KOINSLOT-Inc/kywy-hardware/PCB/Renders/Rotation/Kywy Micro Rotation 01.png

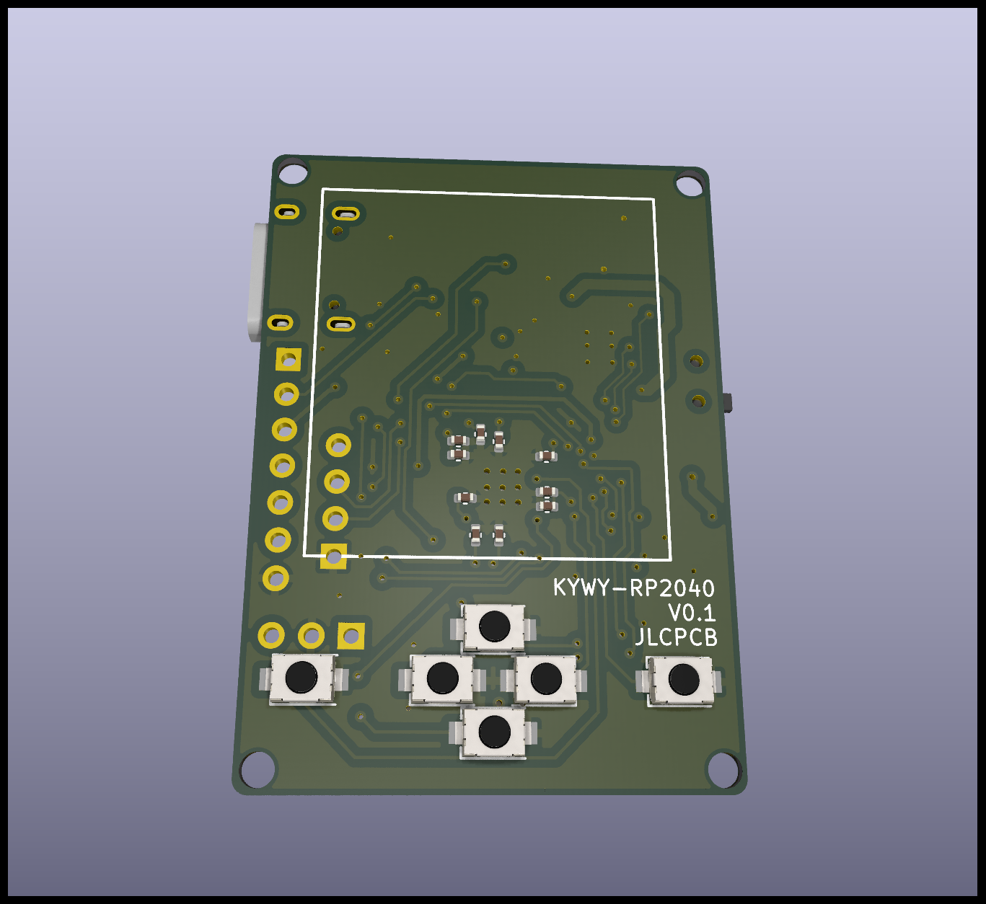
PCB/Renders/Rotation/Kywy Micro Rotation 01.png
