KOINSLOT-Inc/kywy-hardware/PCB/Renders/Rotation/Kywy Micro Rotation 02.png

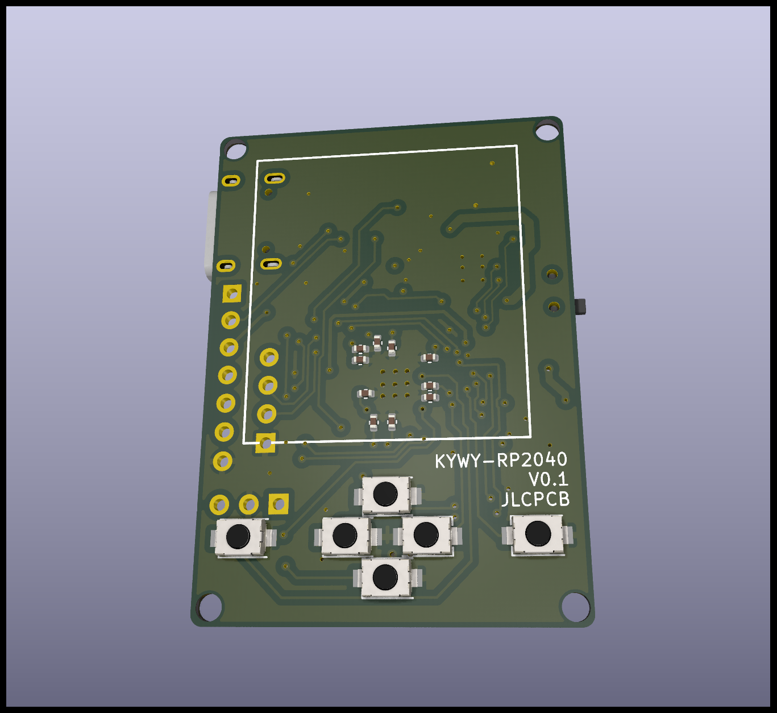
PCB/Renders/Rotation/Kywy Micro Rotation 02.png
