KOINSLOT-Inc/kywy-hardware/PCB/Renders/Rotation/Kywy Micro Rotation 04.png

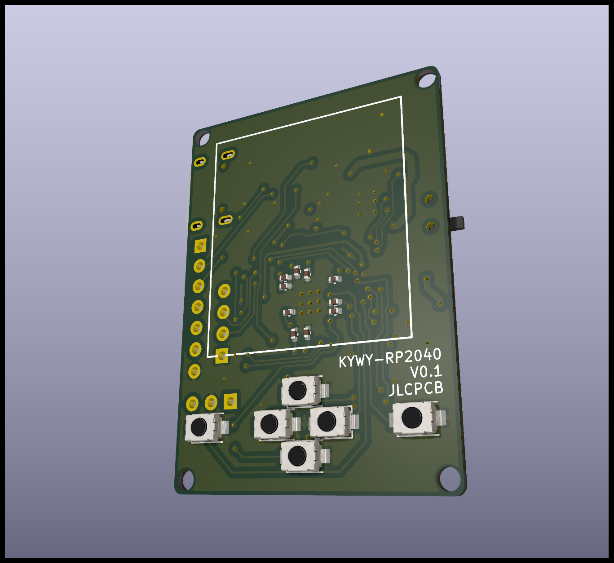
PCB/Renders/Rotation/Kywy Micro Rotation 04.png
