KOINSLOT-Inc/kywy-hardware/PCB/Renders/Rotation/Kywy Micro Rotation 06.png

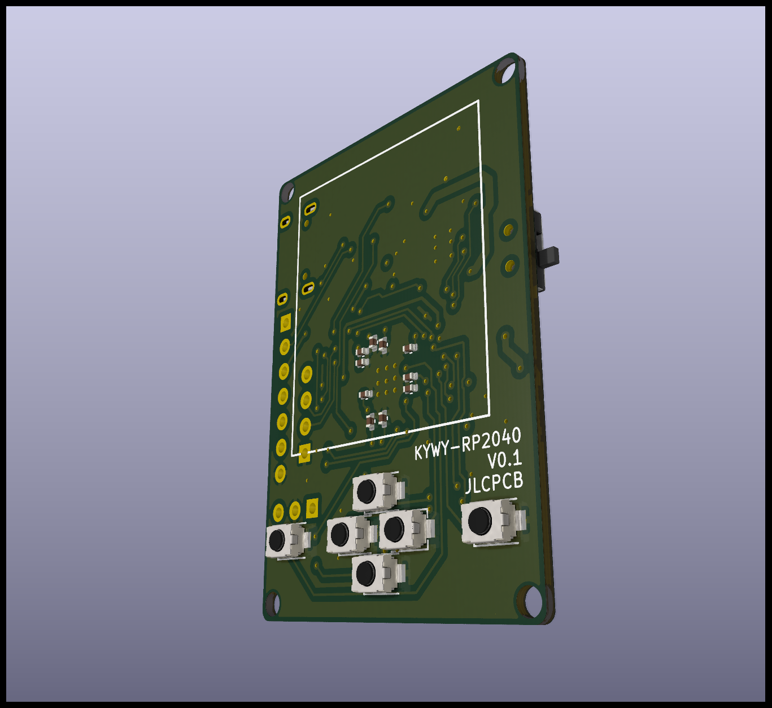
PCB/Renders/Rotation/Kywy Micro Rotation 06.png
