KOINSLOT-Inc/kywy-hardware/PCB/Renders/Rotation/Kywy Micro Rotation 07.png

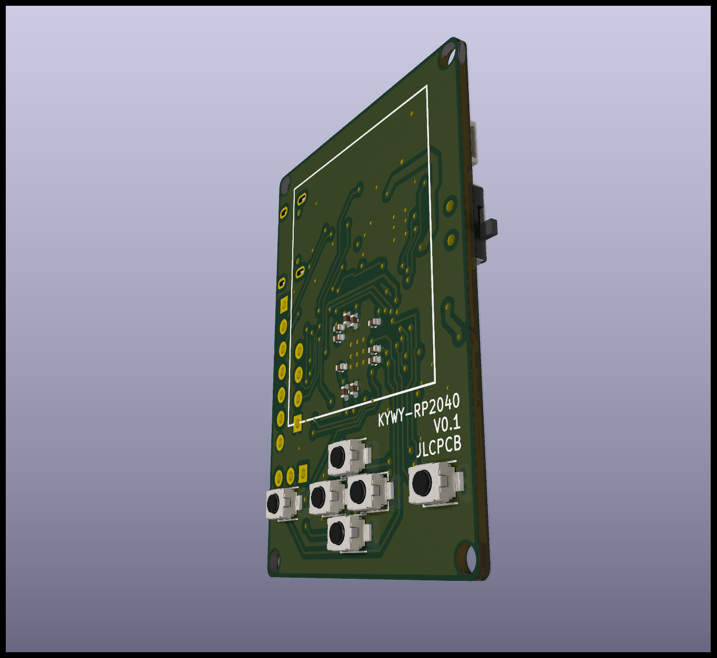
PCB/Renders/Rotation/Kywy Micro Rotation 07.png
