KOINSLOT-Inc/kywy-hardware/PCB/Renders/Rotation/Kywy Micro Rotation 08.png

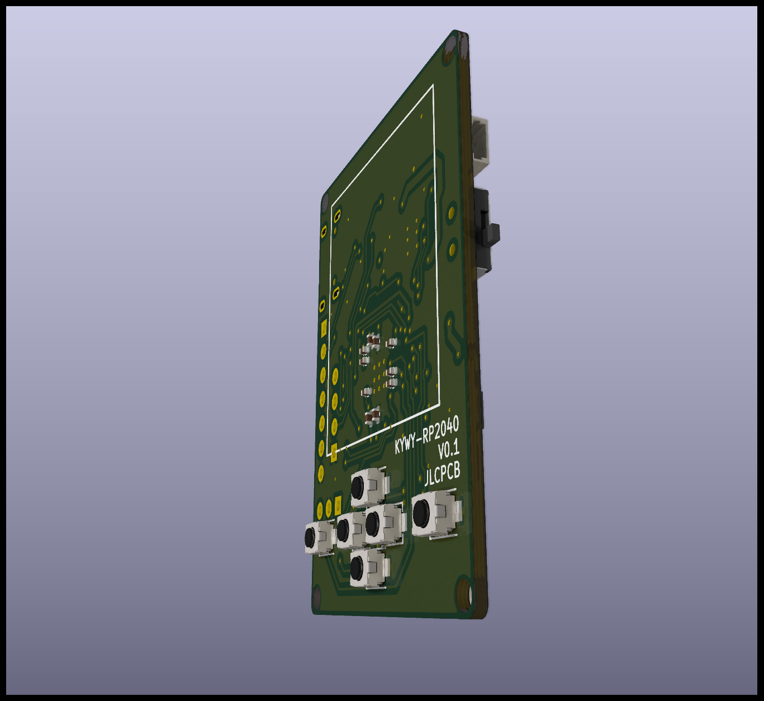
PCB/Renders/Rotation/Kywy Micro Rotation 08.png
