KOINSLOT-Inc/kywy-hardware/PCB/Renders/Rotation/Kywy Micro Rotation 09.png

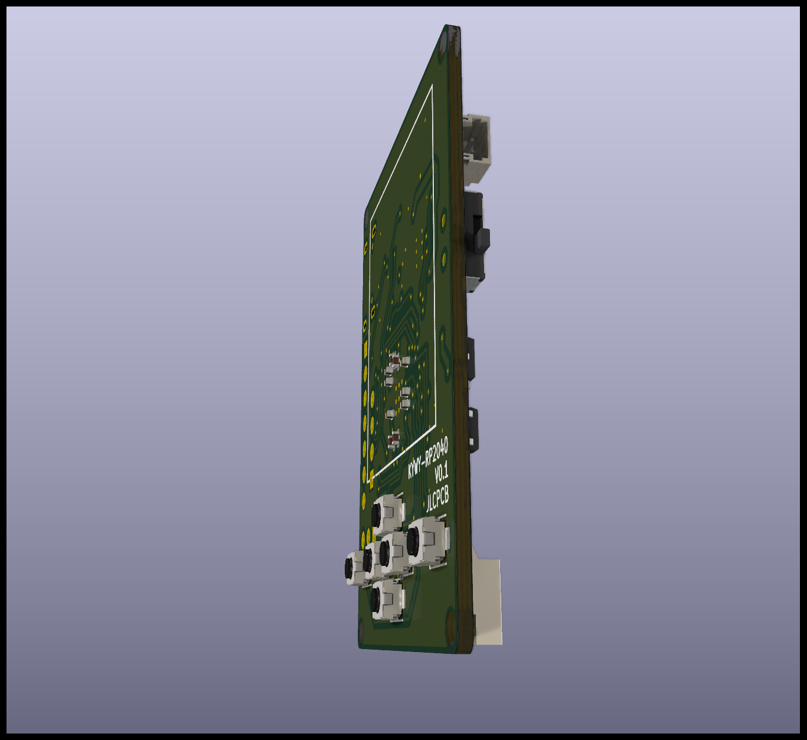
PCB/Renders/Rotation/Kywy Micro Rotation 09.png
