KOINSLOT-Inc/kywy-hardware/PCB/Renders/Rotation/Kywy Micro Rotation 12.png

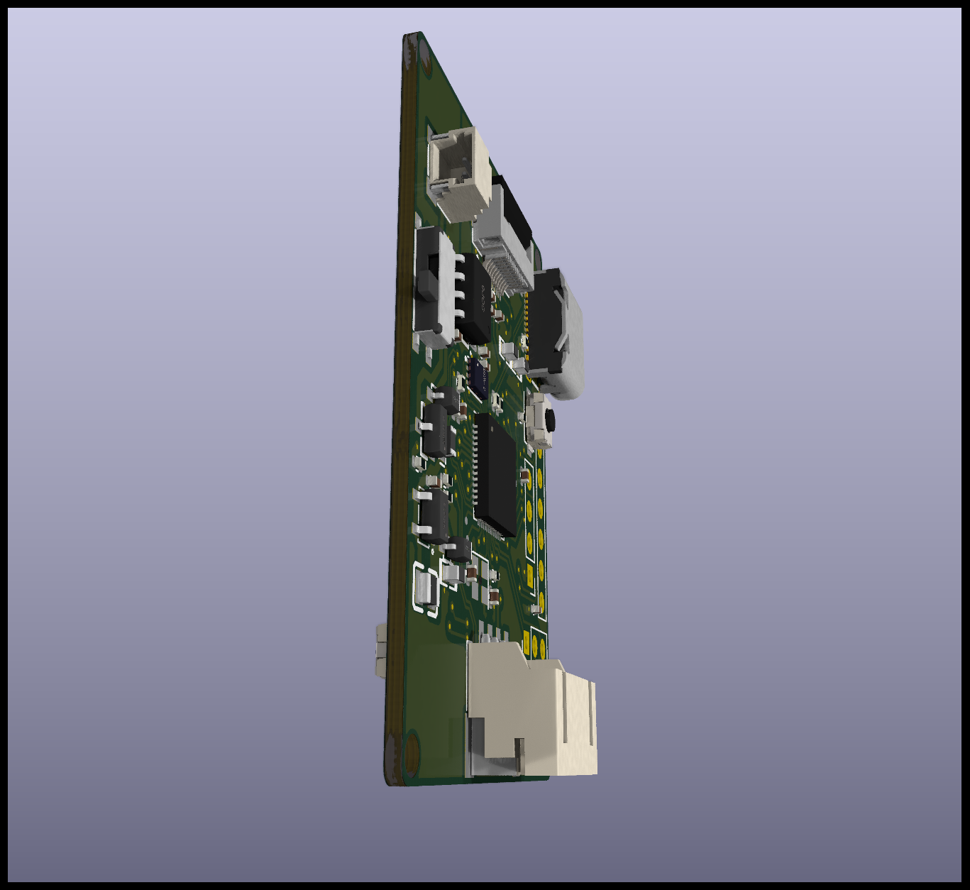
PCB/Renders/Rotation/Kywy Micro Rotation 12.png
