KOINSLOT-Inc/kywy-hardware/PCB/Renders/Rotation/Kywy Micro Rotation 13.png

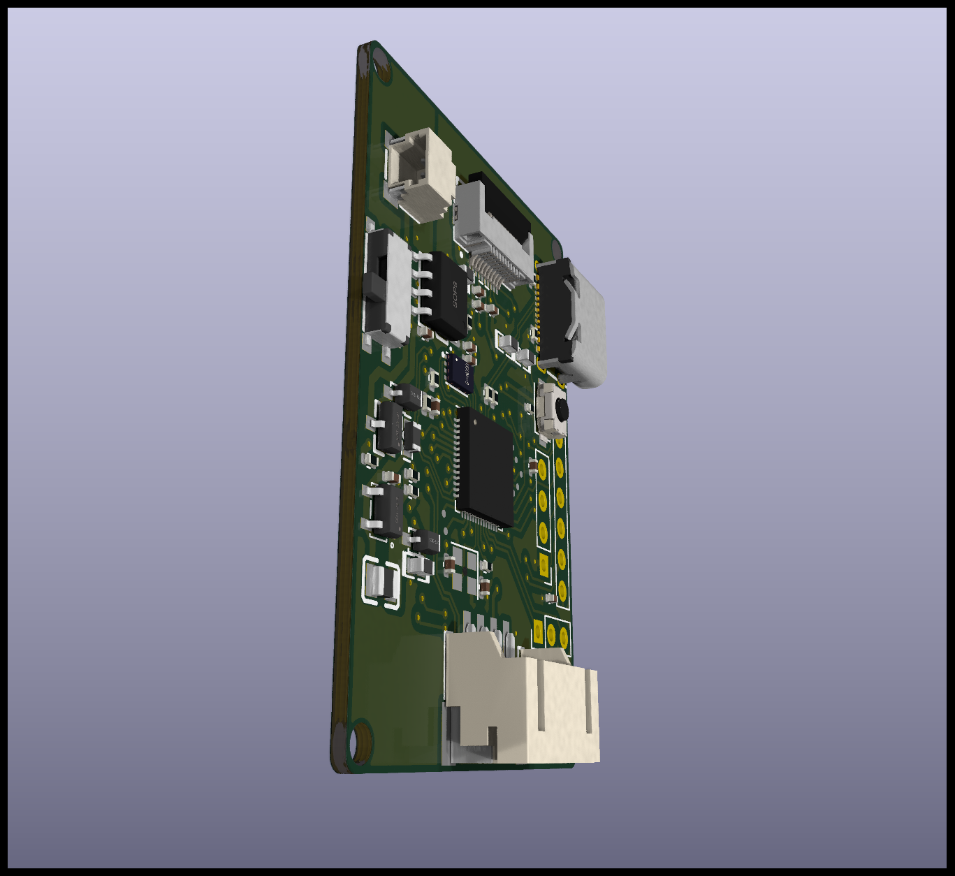
PCB/Renders/Rotation/Kywy Micro Rotation 13.png
