KOINSLOT-Inc/kywy-hardware/PCB/Renders/Rotation/Kywy Micro Rotation 16.png

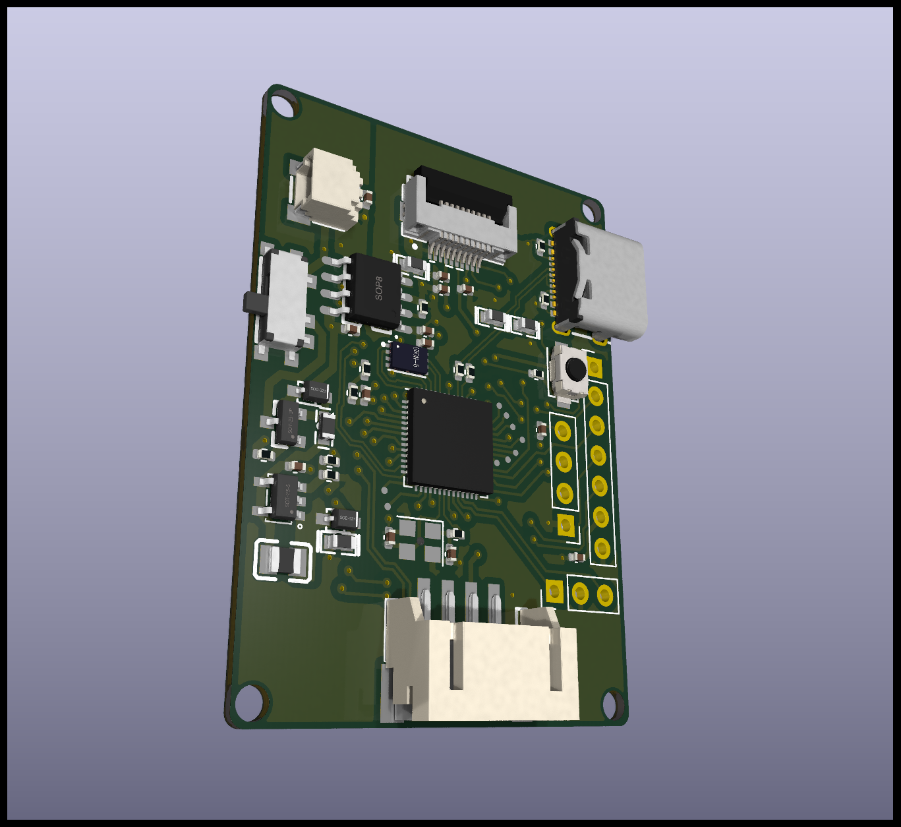
PCB/Renders/Rotation/Kywy Micro Rotation 16.png
