KOINSLOT-Inc/kywy-hardware/PCB/Renders/Rotation/Kywy Micro Rotation 22.png

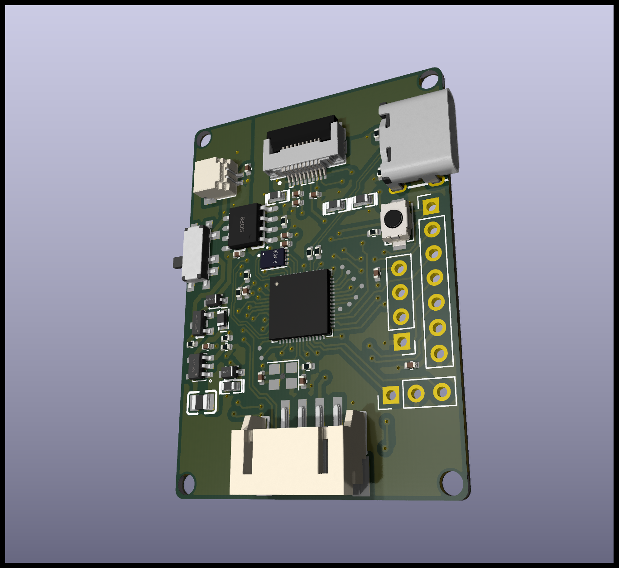
PCB/Renders/Rotation/Kywy Micro Rotation 22.png
