KOINSLOT-Inc/kywy-hardware/PCB/Renders/Rotation/Kywy Micro Rotation 23.png

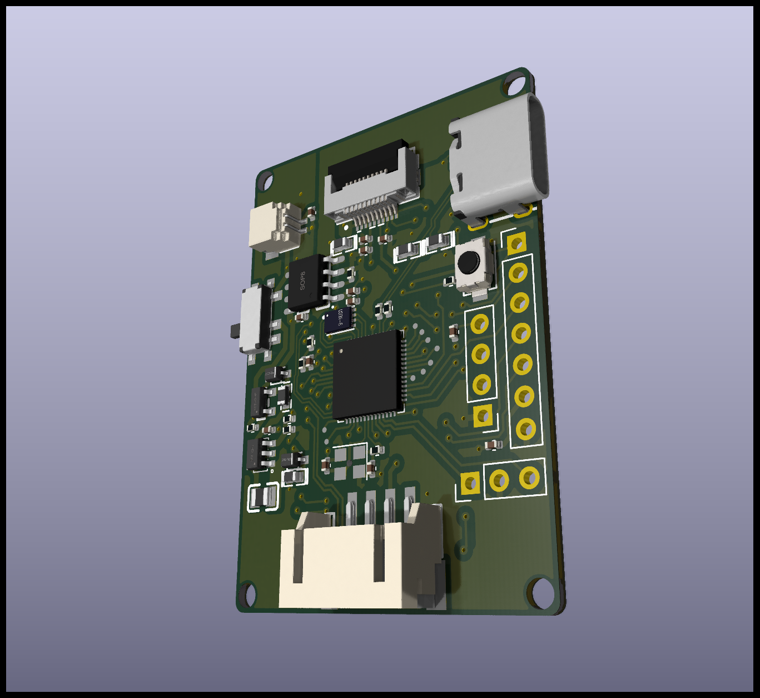
PCB/Renders/Rotation/Kywy Micro Rotation 23.png
