KOINSLOT-Inc/kywy-hardware/PCB/Renders/Rotation/Kywy Micro Rotation 32.png

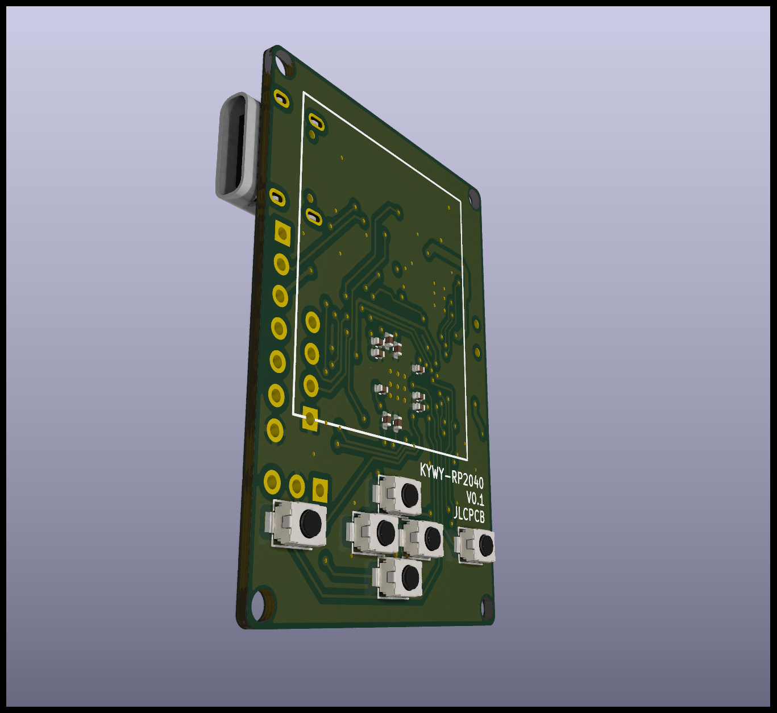
PCB/Renders/Rotation/Kywy Micro Rotation 32.png
