KOINSLOT-Inc/kywy-hardware/PCB/Renders/Rotation/Kywy Micro Rotation 34.png

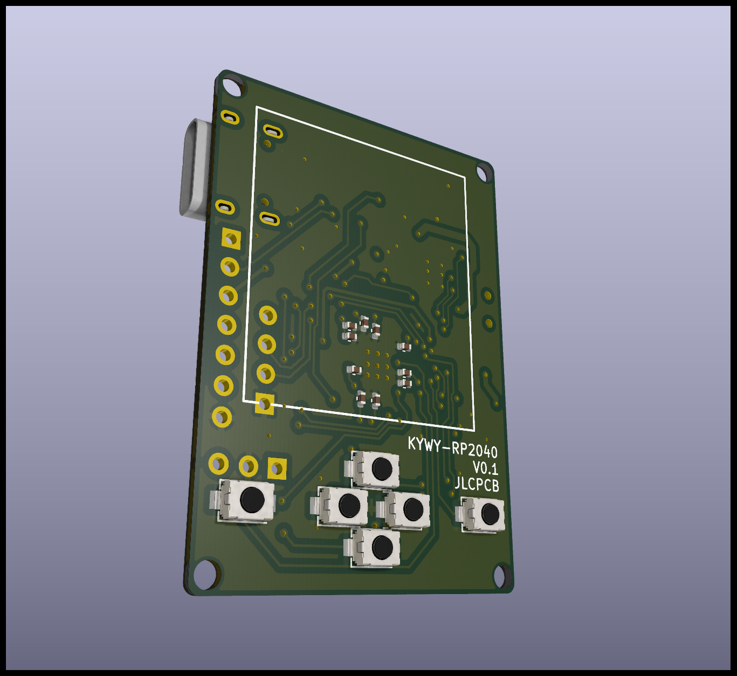
PCB/Renders/Rotation/Kywy Micro Rotation 34.png
